mike-s123/MStar-WLAN/data-small/ctl/Nocontroller.png

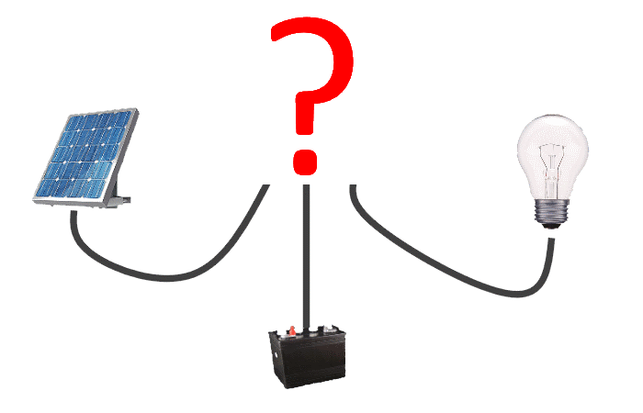
data-small/ctl/Nocontroller.png
