mike-s123/MStar-WLAN/data-small/ctl/PS-MPPT.png

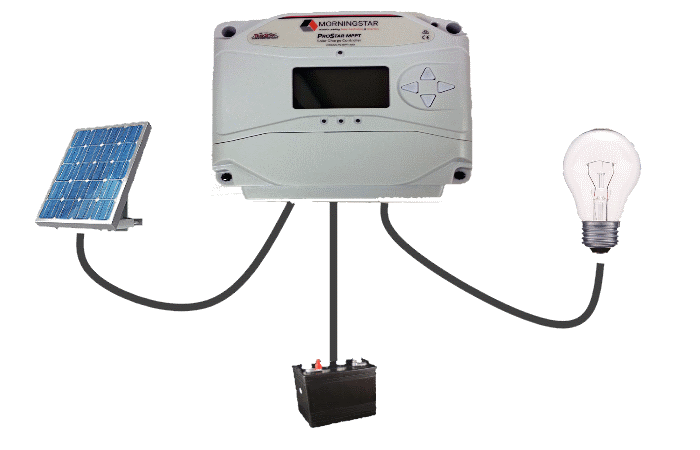
data-small/ctl/PS-MPPT.png
