mike-s123/MStar-WLAN/data-small/ctl/SS-MPPT.png

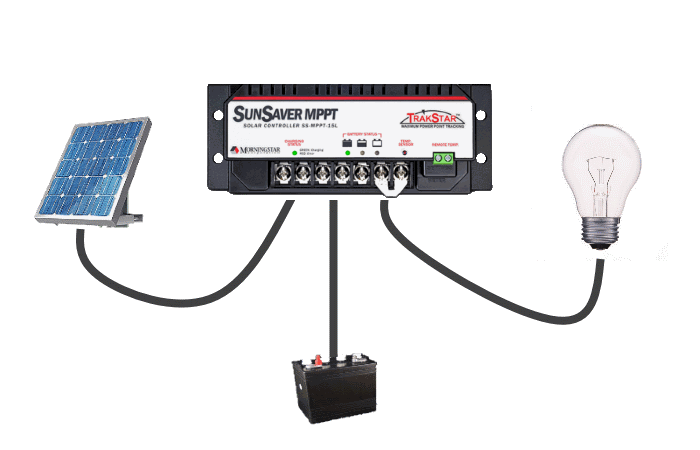
data-small/ctl/SS-MPPT.png
