mike-s123/MStar-WLAN/data-small/ctl/TS-600.png

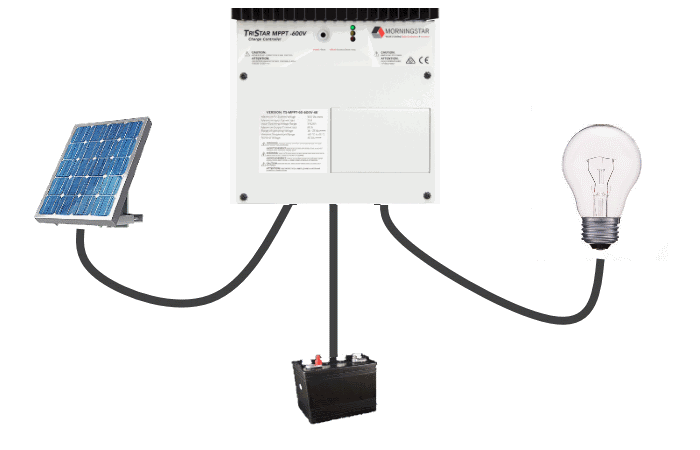
data-small/ctl/TS-600.png
