mike-s123/MStar-WLAN/data/ctl/Nocontroller.png

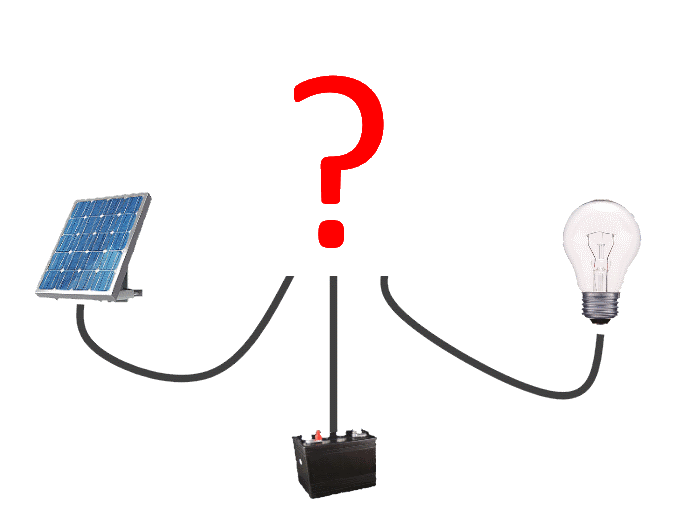
data/ctl/Nocontroller.png
