mike-s123/MStar-WLAN/data/ctl/PS-MPPT.png

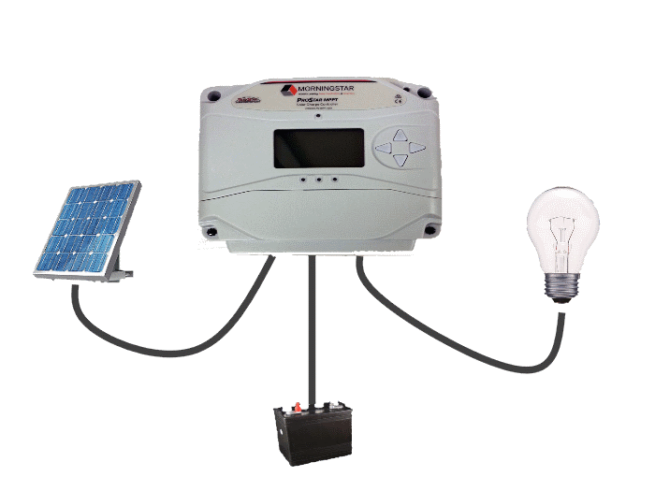
data/ctl/PS-MPPT.png
