mike-s123/MStar-WLAN/data/ctl/SS-MPPT.png

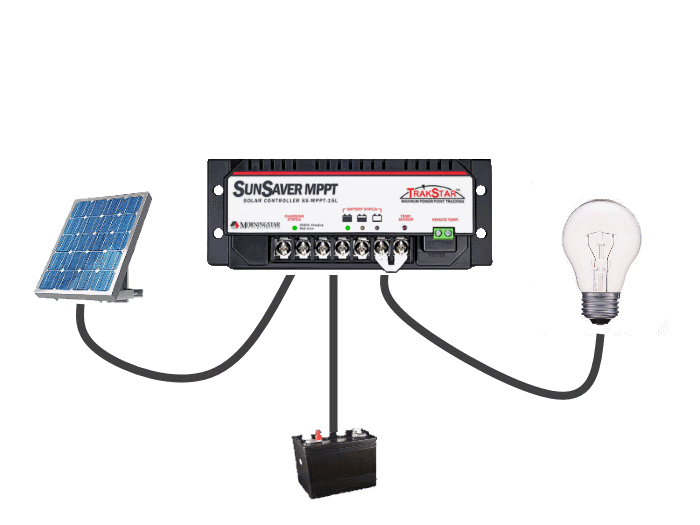
data/ctl/SS-MPPT.png
