mike-s123/MStar-WLAN/data/ctl/TS-600.png

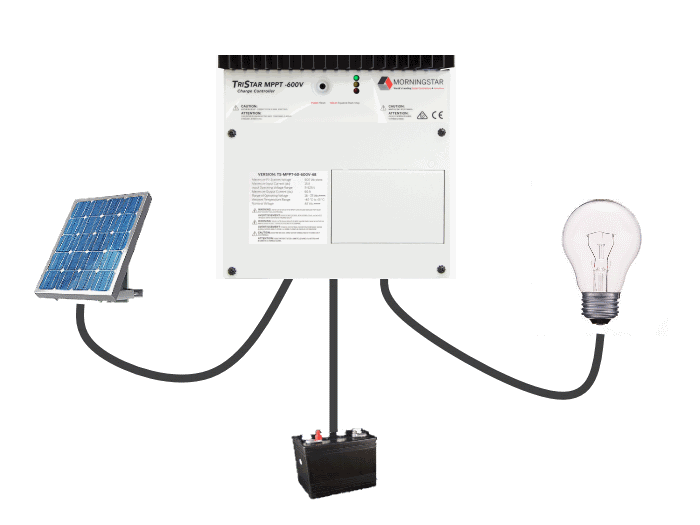
data/ctl/TS-600.png
