mike-s123/MStar-WLAN/data/ctl/TS.png

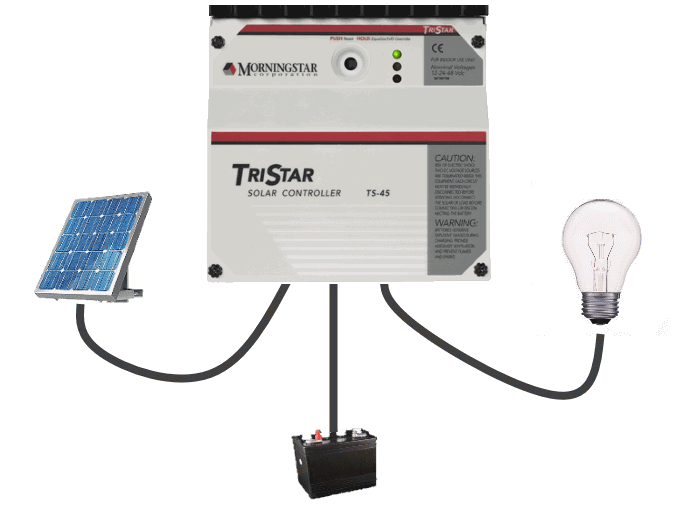
data/ctl/TS.png
