mike-s123/MStar-WLAN/data/img/Schematic.png

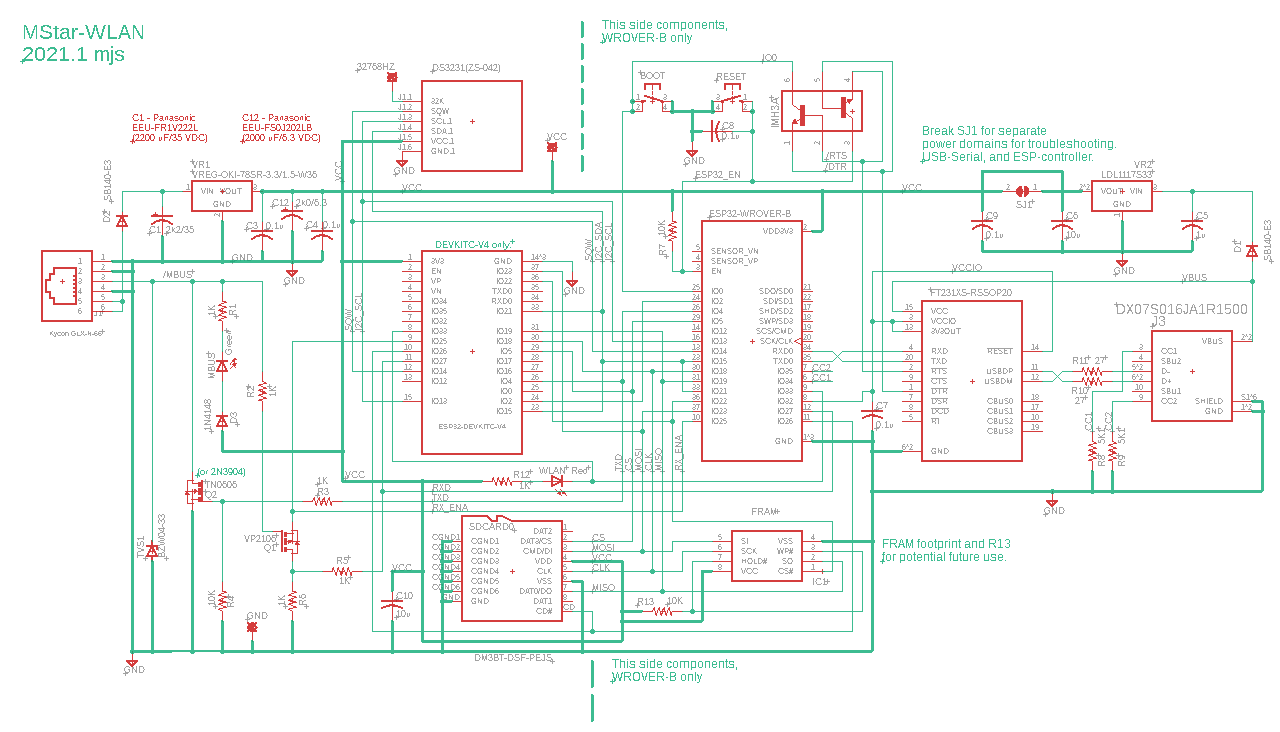
data/img/Schematic.png
