mike-s123/MStar-WLAN/Put on SD Card/img/otherset.png

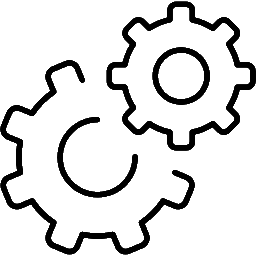
Put on SD Card/img/otherset.png
