mike-s123/MStar-WLAN/Put on SD Card/img/setTime.png

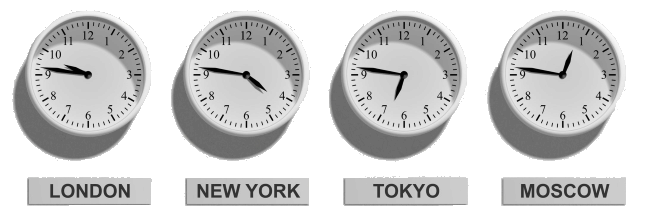
Put on SD Card/img/setTime.png
