mike-s123/MStar-WLAN/Put on SD Card/img/utility.png

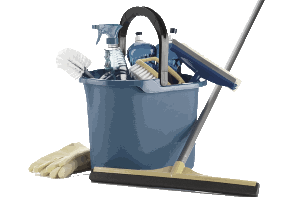
Put on SD Card/img/utility.png
