mike-s123/MStar-WLAN/PROGMEM_FILES.h

//Converted at http://tomeko.net/online_tools/file_to_hex.php?lang=en
// See "PROGMEM files" directory for source files
// currently, OTA.js.gz, local.js, local.css

//File: draw.js, Size: 3435
#define draw_js_len 3435
const uint8_t draw_js[] PROGMEM = {
0x0D, 0x0A, 0x66, 0x75, 0x6E, 0x63, 0x74, 0x69, 0x6F, 0x6E, 0x20, 0x64, 0x72, 0x61, 0x77, 0x28, 
0x29, 0x20, 0x7B, 0x0D, 0x0A, 0x20, 0x20, 0x64, 0x6F, 0x63, 0x75, 0x6D, 0x65, 0x6E, 0x74, 0x2E, 
0x77, 0x72, 0x69, 0x74, 0x65, 0x28, 0x27, 0x3C, 0x64, 0x69, 0x76, 0x20, 0x69, 0x64, 0x3D, 0x22, 
0x63, 0x6F, 0x6E, 0x74, 0x72, 0x6F, 0x6C, 0x6C, 0x65, 0x72, 0x67, 0x72, 0x61, 0x70, 0x68, 0x22, 
0x3E, 0x3C, 0x2F, 0x64, 0x69, 0x76, 0x3E, 0x27, 0x29, 0x3B, 0x0D, 0x0A, 0x20, 0x20, 0x66, 0x6E, 
0x61, 0x6D, 0x65, 0x3D, 0x22, 0x2F, 0x63, 0x6F, 0x6E, 0x74, 0x72, 0x6F, 0x6C, 0x6C, 0x65, 0x72, 
0x2E, 0x72, 0x72, 0x64, 0x22, 0x3B, 0x0D, 0x0A, 0x20, 0x20, 0x66, 0x6E, 0x61, 0x6D, 0x65, 0x64, 
0x3D, 0x22, 0x2F, 0x63, 0x6F, 0x6E, 0x74, 0x72, 0x6F, 0x6C, 0x6C, 0x65, 0x72, 0x64, 0x2E, 0x72, 
0x72, 0x64, 0x22, 0x3B, 0x0D, 0x0A, 0x0D, 0x0A, 0x20, 0x20, 0x76, 0x61, 0x72, 0x20, 0x67, 0x72, 
0x61, 0x70, 0x68, 0x5F, 0x6F, 0x70, 0x74, 0x69, 0x6F, 0x6E, 0x73, 0x20, 0x3D, 0x20, 0x7B, 0x0D, 
0x0A, 0x20, 0x20, 0x20, 0x20, 0x6C, 0x65, 0x67, 0x65, 0x6E, 0x64, 0x3A, 0x20, 0x7B, 0x70, 0x6F, 
0x73, 0x69, 0x74, 0x69, 0x6F, 0x6E, 0x3A, 0x22, 0x6E, 0x77, 0x22, 0x2C, 0x6E, 0x6F, 0x43, 0x6F, 
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
0x52, 0x49, 0x43, 0x6F, 0x6D, 0x70, 0x6F, 0x6E, 0x65, 0x6E, 0x74, 0x28, 0x74, 0x29, 0x2B, 0x22, 
0x26, 0x76, 0x65, 0x72, 0x73, 0x69, 0x6F, 0x6E, 0x3D, 0x22, 0x2B, 0x4D, 0x61, 0x74, 0x68, 0x2E, 
0x72, 0x61, 0x6E, 0x64, 0x6F, 0x6D, 0x28, 0x29, 0x2C, 0x6F, 0x3D, 0x6E, 0x65, 0x77, 0x20, 0x58, 
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
};
