mike-s123/MStar-WLAN/OTA.h

/*
 
  OTA.h is based on  https://github.com/ayushsharma82/AsyncElegantOTA (v 2.2.5), MIT license
  portions are also used in the OTA.js file in the data directory

MIT License

Copyright (c) 2019 Ayush Sharma

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
THE SOFTWARE IS PROVIDED "AS IS", WITHOUT WARRANTY OF ANY KIND, EXPRESS OR
IMPLIED, INCLUDING BUT NOT LIMITED TO THE WARRANTIES OF MERCHANTABILITY,
FITNESS FOR A PARTICULAR PURPOSE AND NONINFRINGEMENT. IN NO EVENT SHALL THE
AUTHORS OR COPYRIGHT HOLDERS BE LIABLE FOR ANY CLAIM, DAMAGES OR OTHER
LIABILITY, WHETHER IN AN ACTION OF CONTRACT, TORT OR OTHERWISE, ARISING FROM,
OUT OF OR IN CONNECTION WITH THE SOFTWARE OR THE USE OR OTHER DEALINGS IN THE
SOFTWARE.
 */

#ifndef asynchOTA_h
#define asynchOTA_h

#include "Arduino.h"
#include "stdlib_noniso.h"
#include "WiFi.h"
#include "AsyncTCP.h"
#include "Update.h"
#include "ESPAsyncWebServer.h"
#include "FS.h"

class AsyncMyOtaClass{

    public:

        void setID(const char* id){
            _id = id;
        }
 
         void begin(AsyncWebServer *server, const char* username = "", const char* password = ""){
            _server = server;

            if(strlen(username) > 0){
                _authRequired = true;
                _username = username;
                _password = password;
            }else{
                _authRequired = false;
                _username = "";
                _password = "";
            }

            _server->on("/update/identity", HTTP_GET, [&](AsyncWebServerRequest *request){
                if(_authRequired){
                    if(!request->authenticate(_username.c_str(), _password.c_str())){
                        return request->requestAuthentication();
                    }
                }
                request->send(200, "application/json", "{\"id\": \""+_id+"\", \"hardware\": \"ESP32\"}");
            });

            _server->on("/update", HTTP_POST, [&](AsyncWebServerRequest *request) {
                if(_authRequired){
                    if(!request->authenticate(_username.c_str(), _password.c_str())){
                        return request->requestAuthentication();
                    }
                }
                // the request handler is triggered after the upload has finished... 
                // create the response, add header, and send response
                AsyncWebServerResponse *response = request->beginResponse((Update.hasError())?500:200, "text/plain", (Update.hasError())?"FAIL":"OK");
                response->addHeader("Connection", "close");
                response->addHeader("Access-Control-Allow-Origin", "*");
                request->send(response);
                restartRequired = true;
         
            }, [&](AsyncWebServerRequest *request, String filename, size_t index, uint8_t *data, size_t len, bool final) {
                //Upload handler chunks in data
                if(_authRequired){
                    if(!request->authenticate(_username.c_str(), _password.c_str())){
                        return request->requestAuthentication();
                    }
                }

                if (!index) {
                  if(!request->hasParam("MD5", true)) {
                      return request->send(400, "text/plain", "MD5 parameter missing");
                  }

                  if(!Update.setMD5(request->getParam("MD5", true)->value().c_str())) {
                      return request->send(400, "text/plain", "MD5 parameter invalid");
                  }
                  
                  debugMsgln("OTA filename: "+filename,2);
                  String fs_name_id;
                  if (FS_NAME == "littlefs") {
                    fs_name_id = F(".littlefs.bin");
                  } else {
                    fs_name_id = F(".spiffs.bin");
                  }
                  int cmd = (filename.indexOf(fs_name_id) > -1 ) ? U_SPIFFS : U_FLASH;
                  if (cmd == U_FLASH && !(filename.indexOf(F("esp32.bin")) > -1) ) {
                    debugMsgln(F("OTA bad filename"),2);
                    return request->send(400, "text/plain", "OTA bad filename or type");; // wrong image for ESP32
                  }
                  myWDT = 360; // allow up to 6 minutes to flash
                  if (cmd == U_FLASH) {
                    myWDT = 120; // allow up to 2 minutes to flash
                    debugMsgln(F("Flash OTA"),1);
                  } else {
                    myWDT = 420; // allow up to 7 minutes to flash
                    debugMsgln(F("Filesystem OTA"),1);
                  }
                  if (logFile) logFile.flush();
                  if (!Update.begin(UPDATE_SIZE_UNKNOWN, cmd)) { // Start with max available size
//                    Update.printError(Serial);
                    return request->send(400, "text/plain", "OTA could not begin");
                  } 
                } // !index

                // Write chunked data to the free sketch space
                if(len){
                    if (Update.write(data, len) != len) {
                        return request->send(400, "text/plain", "OTA could not begin");
                    }
                }
                    
                if (final) { // if the final flag is set then this is the last frame of data
                    if (!Update.end(true)) { //true to set the size to the current progress
                        Update.printError(Serial);
                        return request->send(400, "text/plain", "Could not end OTA");
                    }
                }else{
                    return;
                }
            });
        }

        void loop(){
            if(restartRequired) reboot();
        }

    private:
        AsyncWebServer *_server;

        String getID(){
            String id = "";
            id = String((uint32_t)ESP.getEfuseMac(), HEX);
            id.toUpperCase();
            return id;
        }

        String _id = getID();
        String _username = "";
        String _password = "";
        bool _authRequired = false;
        bool restartRequired = false;

};

AsyncMyOtaClass asynchOTA;
#endif
